kumamuk-git/roBa/doc/img/koro3.JPG

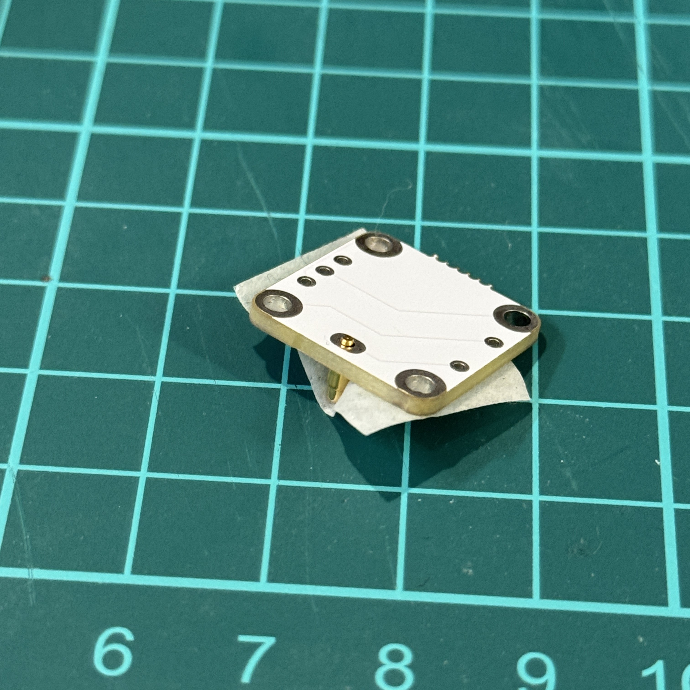
doc/img/koro3.JPG
