kumamuk-git/roBa/doc/img/koro4.JPG

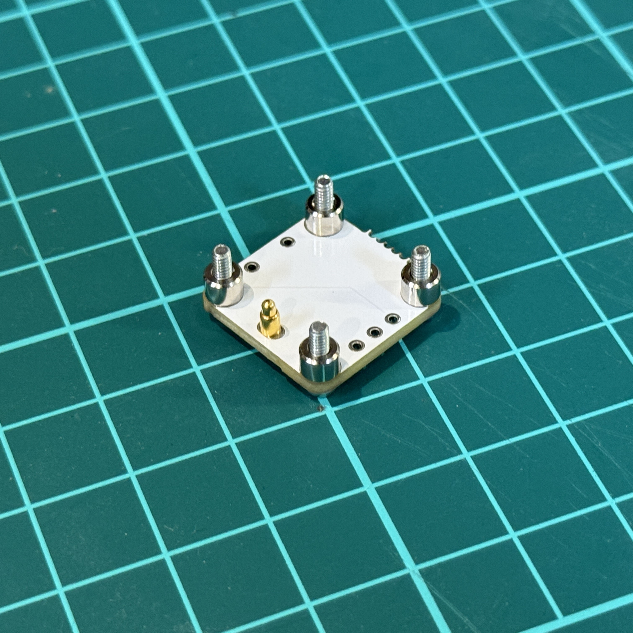
doc/img/koro4.JPG
