kumamuk-git/roBa/doc/img/mac_error.png

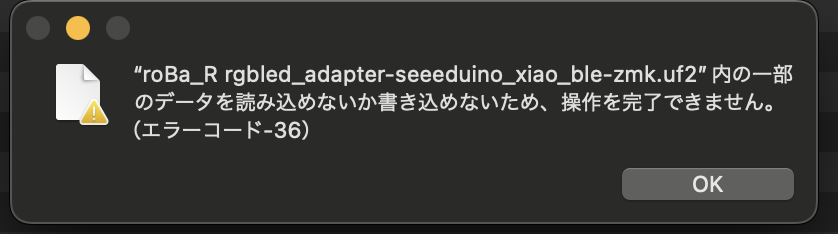
doc/img/mac_error.png
