kumamuk-git/roBa/doc/img/roBa_Natu.jpg

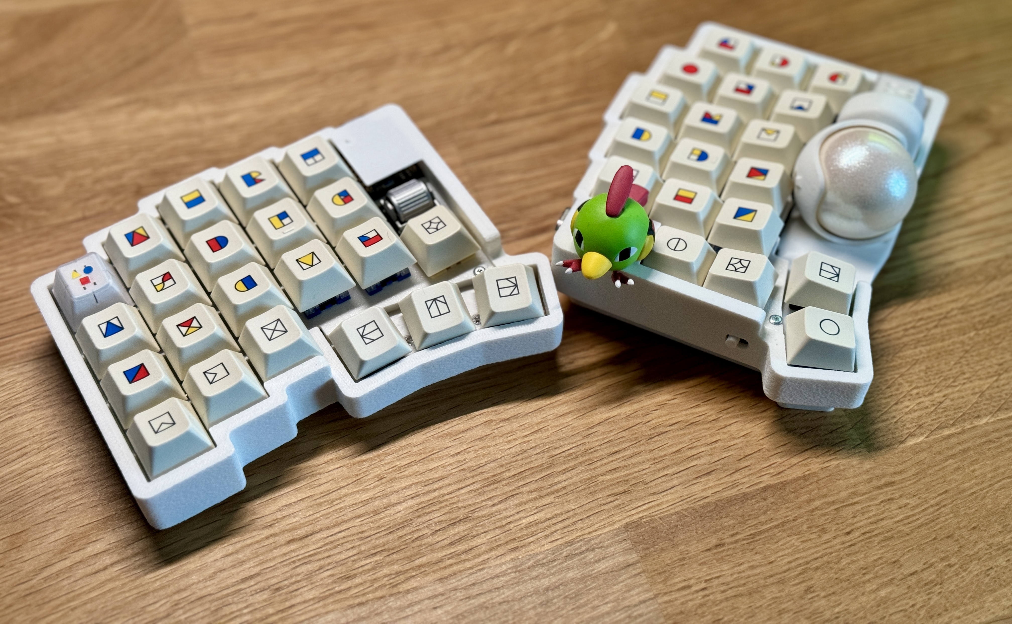
doc/img/roBa_Natu.jpg
